Pfannex/ADE7953_Breakoutboard/Pics/AP_config.PNG

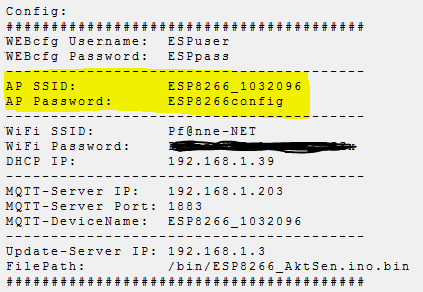
Pics/AP_config.PNG
