Pfannex/ADE7953_Breakoutboard/Pics/Cal_Energy_Graph.jpeg

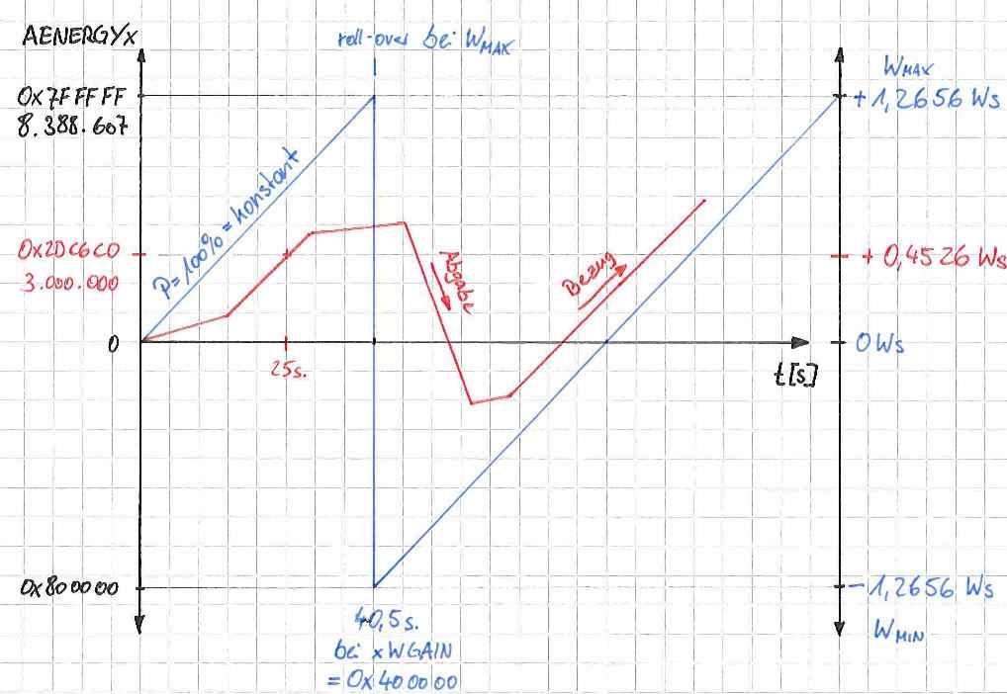
Pics/Cal_Energy_Graph.jpeg
