Pfannex/ADE7953_Breakoutboard/Pics/PGA.PNG

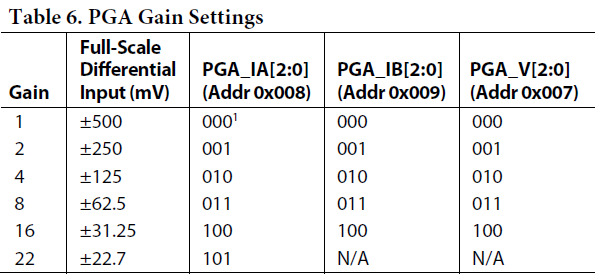
Pics/PGA.PNG
