Pfannex/ADE7953_Breakoutboard/Pics/read_return.PNG

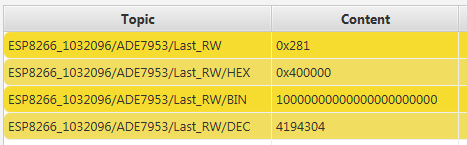
Pics/read_return.PNG
