Pfannex/ADE7953_Breakoutboard/Pics/WebIF_all.PNG

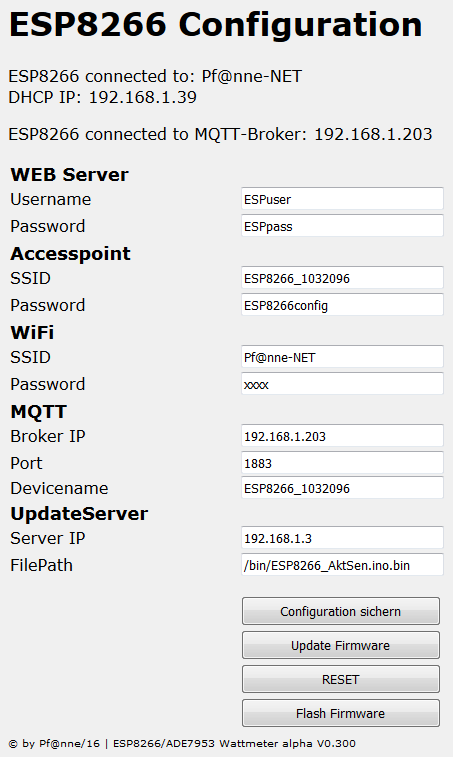
Pics/WebIF_all.PNG
