Pfannex/ADE7953_Breakoutboard/Pics/writeBit_return.PNG

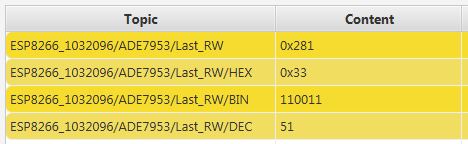
Pics/writeBit_return.PNG
