Pfannex/ADE7953_Breakoutboard/ESP8266_Basic_webServer.cpp

/******************************************************************************

  ProjectName: ESP8266 Basic template             ***** *****
  SubTitle   : WebServer routines                *     *     ************
                                                *   **   **   *           *
  Copyright by Pf@nne                          *   *   *   *   *   ****    *
                                               *   *       *   *   *   *   *
  Last modification by:                        *   *       *   *   ****    *
  - Pf@nne (pf@nne-mail.de)                     *   *     *****           *
                                                 *   *        *   *******
  Date    : 03.12.2016                            *****      *   *
  Version : alpha 0.200                                     *   *
  Revison :                                                *****

********************************************************************************/
#include "ESP8266_Basic_webServer.h"

ESP8266_Basic_webServer::ESP8266_Basic_webServer() : webServer(80){ 

  httpUpdater.setup(&webServer); 
 
  webServer.on("/", std::bind(&ESP8266_Basic_webServer::rootPageHandler, this));
  webServer.on("/ADE7953", std::bind(&ESP8266_Basic_webServer::ADE7953PageHandler, this));
  
  webServer.on("/wlan_config", std::bind(&ESP8266_Basic_webServer::wlanPageHandler, this));
  webServer.on("/gpio", std::bind(&ESP8266_Basic_webServer::gpioPageHandler, this));
  //webServer.on("/cfg", std::bind(&ESP8266_Basic_webServer::cfgPageHandler, this));
  webServer.onNotFound(std::bind(&ESP8266_Basic_webServer::handleNotFound, this));
}

//===============================================================================
//  WEB-Server control
//===============================================================================
void ESP8266_Basic_webServer::start(){
  Serial.println("Start WEB-Server");
  
  pinMode(GPIO2, OUTPUT);
  webServer.begin(); 
  Serial.println("HTTP server started");

}
//===> handle WEB-Server <-----------------------------------------------------
void ESP8266_Basic_webServer::handleClient(){
   webServer.handleClient();
}
//===> CFGstruct pointer <-----------------------------------------------------
void ESP8266_Basic_webServer::set_cfgPointer(CFG *p){
  cfg = p;
}
//===> Sesorstruct pointer <---------------------------------------------------
/*void ESP8266_Basic_webServer::set_sensorPointer(TDS18B20_Sensors *p, THTU21_Sensors *q, TBMP180_Sensors *r){
  DS18B20_Sensors = p;
  HTU21_Sensors = q;
  BMP180_Sensors = r;
}*/
//===> Callback for CFGchange <------------------------------------------------
void ESP8266_Basic_webServer::set_saveConfig_Callback(CallbackFunction c){
  saveConfig_Callback = c;
}
//===> Update Firmware <-------------------------------------------------------
void ESP8266_Basic_webServer::updateFirmware(){
  Serial.println("Updating Firmware.......");
  t_httpUpdate_return ret = ESPhttpUpdate.update(cfg->updateServer, 80, cfg->filePath);
  switch(ret) {
    case HTTP_UPDATE_FAILED:
        Serial.println("[update] Update failed.");
        break;
    case HTTP_UPDATE_NO_UPDATES:
        Serial.println("[update] Update no Update.");
        break;
    case HTTP_UPDATE_OK:
        Serial.println("[update] Update ok."); // may not called we reboot the ESP
        break;
  }
}

//===============================================================================
//  HTML handling
//===============================================================================

//===> Sensor Page <-------------------------------------------------------
void ESP8266_Basic_webServer::ADE7953PageHandler(){
 String rm = ""
  
  "<!doctype html> <html>"
  "<head> <meta charset='utf-8'>"
  "<meta http-equiv='refresh' content='5; URL=http://" + String(IPtoString(WiFi.localIP()))  + "/ADE7953'>"
  "<title>ESP8266 Sensoren</title>"
  "</head>"

  "<body><body bgcolor='#F0F0F0'><font face='VERDANA,ARIAL,HELVETICA'> <form> <font face='VERDANA,ARIAL,HELVETICA'>"
  "<b><h1>ADE7953 measurement</h1></b>"
  
  "<b><h3>Voltage / Current</h3></b>";
  
	  rm += "<font face='Courier New'>";
	
	  //rm += "<tab indent=20>";
    rm += "Voltage : </b>";
    rm += "Current A : </b>";
    rm += "Current B : </b>";
    //DS18B20_Sensors->item[i].serial

  rm += "</font></p>"
  "<font face='VERDANA,ARIAL,HELVETICA'> <b><h3>Power</h3></b> </font>";
  
    rm += "Power : </b>";
    rm += "Q : </b>";
    rm += "S : </b>";


  rm += "</font></p>"
  "<font face='VERDANA,ARIAL,HELVETICA'><font size='-2'>&copy; by Pf@nne/16   |   " + String(cfg->version) + "</font>"
  "</body bgcolor> </body></font>"
  "</html>"  
  ;

  webServer.send(200, "text/html", rm);

}

//#############################################################################
void ESP8266_Basic_webServer::rootPageHandler()
{
  // Check if there are any GET parameters
  if (webServer.hasArg("webUser")) strcpy(cfg->webUser, webServer.arg("webUser").c_str());
  if (webServer.hasArg("webPassword")) strcpy(cfg->webPassword, webServer.arg("webPassword").c_str());
  if (webServer.hasArg("apName")) strcpy(cfg->apName, webServer.arg("apName").c_str());
  if (webServer.hasArg("apPassword")) strcpy(cfg->apPassword, webServer.arg("apPassword").c_str());
  if (webServer.hasArg("wifiSSID")) strcpy(cfg->wifiSSID, webServer.arg("wifiSSID").c_str());
  if (webServer.hasArg("wifiPSK")) strcpy(cfg->wifiPSK, webServer.arg("wifiPSK").c_str());
  if (webServer.hasArg("wifiIP")) strcpy(cfg->wifiIP, webServer.arg("wifiIP").c_str());
  if (webServer.hasArg("mqttServer")) strcpy(cfg->mqttServer, webServer.arg("mqttServer").c_str());
  if (webServer.hasArg("mqttPort")) strcpy(cfg->mqttPort, webServer.arg("mqttPort").c_str());
  if (webServer.hasArg("mqttDeviceName")) strcpy(cfg->mqttDeviceName, webServer.arg("mqttDeviceName").c_str());
  if (webServer.hasArg("updateServer")) strcpy(cfg->updateServer, webServer.arg("updateServer").c_str());
  if (webServer.hasArg("filePath")) strcpy(cfg->filePath, webServer.arg("filePath").c_str());
  

  String rm = ""
  
  "<!doctype html> <html>"
  "<head> <meta charset='utf-8'>"
  "<title>ESP8266 Configuration</title>"
  "</head>"

  "<body><body bgcolor='#F0F0F0'><font face='VERDANA,ARIAL,HELVETICA'> <form> <font face='VERDANA,ARIAL,HELVETICA'>"
  "<b><h1>ESP8266 Configuration</h1></b>";

  if (WiFi.status() == WL_CONNECTED){
    rm += "ESP8266 connected to: "; rm += WiFi.SSID(); rm += "<br>";
    rm += "DHCP IP: "; rm += String(IPtoString(WiFi.localIP())); rm += "<p></p>";
  }else{
    rm += "ESP8266 ist not connected!"; rm += "<p></p>";
  }	
  
  String str = String(cfg->mqttStatus);
  if (str == "connected"){
    rm += "ESP8266 connected to MQTT-Broker: "; rm += cfg->mqttServer; rm += "<p></p>";
  }

  rm += ""
  "<table width='30%' border='0' cellpadding='0' cellspacing='2'>"
  " <tr>"
  "  <td><b><font size='+1'>WEB Server</font></b></td>"
  "  <td></td>"
  " </tr>"
  " <tr>"
  "  <td>Username</td>"
  "  <td><input type='text' id='webUser' name='webUser' value='" + String(cfg->webUser) + "' size='30' maxlength='40' placeholder='Username'></td>"
  " </tr>"
  " <tr>"
  " <tr>"
  "  <td>Password</td>"
  "  <td><input type='text' id='webPassword' name='webPassword' value='" + String(cfg->webPassword) + "' size='30' maxlength='40' placeholder='Password'></td>"
  " </tr>"
  " <tr>"

  " <tr>"
  "  <td><b><font size='+1'>Accesspoint</font></b></td>"
  "  <td></td>"
  " </tr>"
  " <tr>"
  "  <td>SSID</td>"
  "  <td><input type='text' id='apName' name='apName' value='" + String(cfg->apName) + "' size='30' maxlength='40' placeholder='SSID'></td>"
  " </tr>"
  " <tr>"
  " <tr>"
  "  <td>Password</td>"
  "  <td><input type='text' id='apPassword' name='apPassword' value='" + String(cfg->apPassword) + "' size='30' maxlength='40' placeholder='Password'></td>"
  " </tr>"
  " <tr>"

  " <tr>"
  "  <td><b><font size='+1'>WiFi</font></b></td>"
  "  <td></td>"
  " </tr>"
  "  <td>SSID</td>"
  "  <td><input type='text' id='wifiSSID' name='wifiSSID' value='" + String(cfg->wifiSSID) + "' size='30' maxlength='40' placeholder='SSID'></td>"
  " </tr>"
  " <tr>"
  " <tr>"
  "  <td>Password</td>"
  "  <td><input type='text' id='wifiPSK' name='wifiPSK' value='" + String(cfg->wifiPSK) + "' size='30' maxlength='40' placeholder='Password'></td>"
  " </tr>"
  " <tr>"

  " <tr>"
  "  <td><b><font size='+1'>MQTT</font></b></td>"
  "  <td></td>"
  " </tr>"
  " <tr>"
  "  <td>Broker IP</td>"
  "  <td><input type='text' id='mqttServer' name='mqttServer' value='" + String(cfg->mqttServer) + "' size='30' maxlength='40' placeholder='IP Address'></td>"
  " </tr>"
  " <tr>"
  " <tr>"
  "  <td>Port</td>"
  "  <td><input type='text' id='mqttPort' name='mqttPort' value='" + String(cfg->mqttPort) + "' size='30' maxlength='40' placeholder='Port'></td>"
  " </tr>"
  " <tr>"
  "  <td>Devicename</td>"
  "  <td><input type='text' id='mqttDeviceName' name='mqttDeviceName' value='" + String(cfg->mqttDeviceName) + "' size='30' maxlength='40' placeholder='Devicename'></td>"
  " </tr>"

  " <tr>"
  "  <td><b><font size='+1'>UpdateServer</font></b></td>"
  "  <td></td>"
  " </tr>"
  " <tr>"
  "  <td>Server IP</td>"
  "  <td><input type='text' id='updateServer' name='updateServer' value='" + String(cfg->updateServer) + "' size='30' maxlength='40' placeholder='IP Address'></td>"
  " </tr>"
  " <tr>"
  " <tr>"
  "  <td>FilePath</td>"
  "  <td><input type='text' id='filePath' name='filePath' value='" + String(cfg->filePath) + "' size='30' maxlength='40' placeholder='Path'></td>"
  " </tr>"

  " <tr>"
  "  <td><p></p> </td>"
  "  <td>  </td>"
  " </tr>"
  " <tr>"
  "  <td></td>"
  "  <td><input type='submit' value='Configuration sichern' style='height:30px; width:200px' > </font></form> </td>"
  " </tr>"

 " <tr>"
 "  <td></td>"
 "  <td>  </td>"
 " </tr>"
 " <tr>"
 "  <td></td>"
 "  <td><input type='submit' value='Update Firmware' id='update' name='update' value='' style='height:30px; width:200px' ></td>"
 " </tr>"

  " <tr>"
  "  <td></td>"
  "  <td>  </td>"
  " </tr>"
  " <tr>"
  "  <td></td>"
  "  <td><input type='submit' value='RESET' id='reset' name='reset' value='' style='height:30px; width:200px' >  </font></form> </td>"
  " </tr>"

  " <tr>"
  "  <td></td>"
  "  <td>  </td>"
  " </tr>"
  " <tr>"
  "  <td></td>"
  "  <td><input type='button' onclick=\"location.href='./update'\"  value='Flash Firmware' style='height:30px; width:200px' >  </font></form> </td>"
  " </tr>"

  "</table>"

  "<font size='-2'>&copy; by Pf@nne/16   |   " + String(cfg->version) + "</font>"
  "</body bgcolor> </body></font>"
  "</html>"  
  ;

  webServer.send(200, "text/html", rm);
 
  if (saveConfig_Callback != nullptr)
    saveConfig_Callback();
  else
     Serial.println("null");
	 
  if (webServer.hasArg("reset")) ESP.restart();
  if (webServer.hasArg("update")) updateFirmware();
}

//#############################################################################

void ESP8266_Basic_webServer::wlanPageHandler()
{
  // Check if there are any GET parameters
  if (webServer.hasArg("ssid"))
  {    
    if (webServer.hasArg("password"))
    {
      WiFi.begin(webServer.arg("ssid").c_str(), webServer.arg("password").c_str());
    }
    else
    {
      WiFi.begin(webServer.arg("ssid").c_str());
    }
    
    while (WiFi.status() != WL_CONNECTED)
    {
      delay(500);
      Serial.print(".");
    }
      
    Serial.println("");
    Serial.println("WiFi connected");  
    Serial.println("IP address: ");
    Serial.println(WiFi.localIP());

    delay(1000);
  }
  
  String response_message = "";
  response_message += "<html>";
  response_message += "<head><title>ESP8266 Webserver</title></head>";
  response_message += "<body style=\"background-color:PaleGoldenRod\"><h1><center>WLAN Settings</center></h1>";
  
  if (WiFi.status() == WL_CONNECTED)
  {
    response_message += "Status: Connected<br>";
  }
  else
  {
    response_message += "Status: Disconnected<br>";
  }
  
  response_message += "<p>To connect to a WiFi network, please select a network...</p>";

  // Get number of visible access points
  int ap_count = WiFi.scanNetworks();
  
  if (ap_count == 0)
  {
    response_message += "No access points found.<br>";
  }
  else
  {
    response_message += "<form method=\"get\">";

    // Show access points
    for (uint8_t ap_idx = 0; ap_idx < ap_count; ap_idx++)
    {
      response_message += "<input type=\"radio\" name=\"ssid\" value=\"" + String(WiFi.SSID(ap_idx)) + "\">";
      response_message += String(WiFi.SSID(ap_idx)) + " (RSSI: " + WiFi.RSSI(ap_idx) +")";
      (WiFi.encryptionType(ap_idx) == ENC_TYPE_NONE) ? response_message += " " : response_message += "*";
      response_message += "<br><br>";
    }
    
    response_message += "WiFi password (if required):<br>";
    response_message += "<input type=\"text\" name=\"password\"><br>";
    response_message += "<input type=\"submit\" value=\"Connect\">";
    response_message += "</form>";
  }

  response_message += "</body></html>";
  
  webServer.send(200, "text/html", response_message);
}


void ESP8266_Basic_webServer::gpioPageHandler()
{
  // Check if there are any GET parameters
  if (webServer.hasArg("gpio2"))
  { 
    if (webServer.arg("gpio2") == "1")
    {
      digitalWrite(GPIO2, HIGH);
    }
    else
    {
      digitalWrite(GPIO2, LOW);
    }
  }

  String response_message = "<html><head><title>ESP8266 Webserver</title></head>";
  response_message += "<body style=\"background-color:PaleGoldenRod\"><h1><center>Control GPIO pins</center></h1>";
  response_message += "<form method=\"get\">";

  response_message += "GPIO2:<br>";

  if (digitalRead(GPIO2) == LOW)
  {
    response_message += "<input type=\"radio\" name=\"gpio2\" value=\"1\" onclick=\"submit();\">On<br>";
    response_message += "<input type=\"radio\" name=\"gpio2\" value=\"0\" onclick=\"submit();\" checked>Off<br>";
  }
  else
  {
    response_message += "<input type=\"radio\" name=\"gpio2\" value=\"1\" onclick=\"submit();\" checked>On<br>";
    response_message += "<input type=\"radio\" name=\"gpio2\" value=\"0\" onclick=\"submit();\">Off<br>";
  }

  response_message += "</form></body></html>";

  
  webServer.send(200, "text/html", response_message);
}


void ESP8266_Basic_webServer::handleNotFound()
{
  String message = "File Not Found\n\n";
  message += "URI: ";
  message += webServer.uri();
  message += "\nMethod: ";
  message += (webServer.method() == HTTP_GET)?"GET":"POST";
  message += "\nArguments: ";
  message += webServer.args();
  message += "\n";
  
  for (uint8_t i = 0; i < webServer.args(); i++)
  {
    message += " " + webServer.argName(i) + ": " + webServer.arg(i) + "\n";
  }
  
  webServer.send(404, "text/plain", message);
}

//===============================================================================
//  helpers
//===============================================================================

//===> IPToString  <-----------------------------------------------------------
String ESP8266_Basic_webServer::IPtoString(IPAddress ip) {
  String res = "";
  for (int i = 0; i < 3; i++) {
    res += String((ip >> (8 * i)) & 0xFF) + ".";
  }
  res += String(((ip >> 8 * 3)) & 0xFF);
  return res;
}
