Pfannex/ADE7953_Breakoutboard/ESP8266_Basic_data.cpp

/******************************************************************************

  ProjectName: ESP8266 Basic template             ***** *****
  SubTitle   : Data definitions                  *     *     ************
                                                *   **   **   *           *
  Copyright by Pf@nne                          *   *   *   *   *   ****    *
                                               *   *       *   *   *   *   *
  Last modification by:                        *   *       *   *   ****    *
  - Pf@nne (pf@nne-mail.de)                     *   *     *****           *
                                                 *   *        *   *******
  Date    : 03.12.2016                            *****      *   *
  Version : alpha 0.200                                     *   *
  Revison :                                                *****

********************************************************************************/
#include <Arduino.h>
#include "ESP8266_Basic_data.h"

Topics::Topics(){ 

//suscibe
  sub.E1.count = sub_e1;
  sub.E2.count = sub_e2;
  sub.E3.count = sub_e3;
  
  sub.E1.item[0] = "WiFiConfig";
  sub.E2.item[0][0] = "WEBserver";
  sub.E3.item[0][0][0] = "Username";
  sub.E3.item[0][0][1] = "Password";
  sub.E2.item[0][1] = "Accesspoint";
  sub.E3.item[0][1][0] = "SSID";
  sub.E3.item[0][1][1] = "Password";
  sub.E2.item[0][2] = "WiFi";
  sub.E3.item[0][2][0] = "SSID";
  sub.E3.item[0][2][1] = "Password";
  sub.E3.item[0][2][2] = "IP";
  sub.E2.item[0][3] = "MQTT";
  sub.E3.item[0][3][0] = "Server";
  sub.E3.item[0][3][1] = "Port";
  sub.E3.item[0][3][2] = "Status";
  sub.E2.item[0][4] = "UpdateServer";
  sub.E3.item[0][4][0] = "Server";
  sub.E3.item[0][4][1] = "FilePath";
    
  sub.E1.item[1] = "ESP8266";
  sub.E2.item[1][0] = "Control";
  sub.E3.item[1][0][0] = "Reboot";

  sub.E1.item[2] = "ADE7953";
  sub.E2.item[2][0] = "Control";
  sub.E3.item[2][0][1] = "read";
  sub.E3.item[2][0][2] = "write";
  sub.E3.item[2][0][3] = "readBit";
  sub.E3.item[2][0][4] = "writeBit";
  sub.E3.item[2][0][5] = "init";
  sub.E3.item[2][0][6] = "updateTime";
  sub.E3.item[2][0][7] = "saveConfig";
  sub.E3.item[2][0][8] = "setDefault";
  sub.E3.item[2][0][9] = "resetEnergy";
  sub.E2.item[2][1] = "getValues";
  sub.E3.item[2][1][0] = "V_INST";
  sub.E3.item[2][1][1] = "IA_INST";
  sub.E3.item[2][1][2] = "IB_INST";
  sub.E3.item[2][1][3] = "getWaves";
  sub.E3.item[2][1][4] = "SampleRate";
  sub.E3.item[2][1][5] = "Periods";

  sub.E1.item[3] = "File";
  sub.E2.item[3][0] = "Read";
  sub.E3.item[3][0][0] = "Field_01";
  sub.E3.item[3][0][1] = "Field_02";
  sub.E2.item[3][1] = "Write";
  sub.E3.item[3][1][0] = "Field_01";
  sub.E3.item[3][1][1] = "Field_02";

  sub.E1.item[4] = "Relay";
  sub.E2.item[4][0] = "set";
  sub.E2.item[4][1] = "getStatus";

//publish
  pub.E1.count = pub_e1;
  pub.E2.count = pub_e2;
  pub.E3.count = pub_e3;
  
  pub.E1.item[0] = "WiFiConfig";
  pub.E2.item[0][0] = "WEBserver";
  pub.E3.item[0][0][0] = "Username";
  pub.E3.item[0][0][1] = "Password";
  pub.E2.item[0][1] = "Accesspoint";
  pub.E3.item[0][1][0] = "SSID";
  pub.E3.item[0][1][1] = "Password";
  pub.E2.item[0][2] = "WiFi";
  pub.E3.item[0][2][0] = "SSID";
  pub.E3.item[0][2][1] = "Password";
  pub.E3.item[0][2][2] = "IP";
  pub.E2.item[0][3] = "MQTT";
  pub.E3.item[0][3][0] = "Server";
  pub.E3.item[0][3][1] = "Port";
  pub.E3.item[0][3][2] = "Status";
  pub.E2.item[0][4] = "UpdateServer";
  pub.E3.item[0][4][0] = "Server";
  pub.E3.item[0][4][1] = "FilePath";
  
  pub.E1.item[1] = "Control";
  pub.E2.item[1][0] = "Status";
  pub.E3.item[1][0][0] = "WiFi";
  pub.E3.item[1][0][1] = "MQTT";
  pub.E3.item[1][0][2] = "updateFirmware";

  pub.E1.item[2] = "ADE7953";
  pub.E2.item[2][0] = "Last_RW";
  pub.E3.item[2][0][0] = "HEX";
  pub.E3.item[2][0][1] = "BIN";
  pub.E3.item[2][0][2] = "DEC";
  pub.E3.item[2][0][3] = "Bit";
  pub.E3.item[2][0][4] = "value";
  pub.E3.item[2][0][5] = "RegName";
  pub.E2.item[2][1] = "values";
  pub.E3.item[2][1][0] = "V_RMS";
  pub.E3.item[2][1][1] = "IA_RMS";
  pub.E3.item[2][1][2] = "IB_RMS";
  pub.E3.item[2][1][3] = "PFA";
  pub.E3.item[2][1][4] = "PFB";
  pub.E3.item[2][1][5] = "ANGLE_A";
  pub.E3.item[2][1][6] = "ANGLE_B";
  pub.E3.item[2][1][7] = "PERIOD";
  pub.E3.item[2][1][8] = "FREQUENZ";
  pub.E3.item[2][1][9] = "P_A";
  pub.E3.item[2][1][10] = "Q_A";
  pub.E3.item[2][1][11] = "S_A";
  pub.E3.item[2][1][12] = "P_B";
  pub.E3.item[2][1][13] = "Q_B";
  pub.E3.item[2][1][14] = "S_B";
  pub.E3.item[2][1][15] = "IA_INST";
  pub.E3.item[2][1][16] = "IB_INST";
  pub.E3.item[2][1][17] = "V_INST";
  pub.E3.item[2][1][18] = "V_RMSrel";
  pub.E3.item[2][1][19] = "IA_RMSrel";
  pub.E3.item[2][1][20] = "IB_RMSrel";
  pub.E3.item[2][1][21] = "P_Arel";
  pub.E3.item[2][1][22] = "Q_Arel";
  pub.E3.item[2][1][23] = "S_Arel";
  pub.E3.item[2][1][24] = "P_Brel";
  pub.E3.item[2][1][25] = "Q_Brel";
  pub.E3.item[2][1][26] = "S_Brel";
  pub.E3.item[2][1][27] = "W_A";
  pub.E3.item[2][1][28] = "Wb_A";
  pub.E3.item[2][1][29] = "Ws_A";
  pub.E3.item[2][1][30] = "W_B";
  pub.E3.item[2][1][31] = "Wb_B";
  pub.E3.item[2][1][32] = "Ws_B";
  pub.E3.item[2][1][33] = "Time";
  pub.E3.item[2][1][34] = "INSTready";
  pub.E3.item[2][1][35] = "temperature";
  pub.E3.item[2][1][36] = "pressure";

  pub.E1.item[3] = "Relay";
  pub.E2.item[3][0] = "state";



}
