Pfannex/ADE7953_Breakoutboard/ESP8266_Basic_data.h

/******************************************************************************

  ProjectName: ESP8266 Basic template             ***** *****
  SubTitle   : Data Header                       *     *     ************
                                                *   **   **   *           *
  Copyright by Pf@nne                          *   *   *   *   *   ****    *
                                               *   *       *   *   *   *   *
  Last modification by:                        *   *       *   *   ****    *
  - Pf@nne (pf@nne-mail.de)                     *   *     *****           *
                                                 *   *        *   *******
  Date    : 03.12.2016                            *****      *   *
  Version : alpha 0.200                                     *   *
  Revison :                                                *****

********************************************************************************/
#pragma once
#define Version "ESP8266/ADE7953 Wattmeter alpha V0.300"
 
  typedef char* topicField; 

//publish struct
  const int pub_e1 = 5;			//define TreeDepht here!!!
  const int pub_e2 = 6;
  const int pub_e3 = 50;
  const int pub_e4 = 0;
  
  typedef struct Tpub_topicE1{
    topicField item[pub_e1];
	int count;
  };
  typedef struct Tpub_topicE2{
    topicField item[pub_e1][pub_e2];
	int count;
  };
  typedef struct Tpub_topicE3{
    topicField item[pub_e1][pub_e2][pub_e3];
	int count;
  };
 
  typedef struct Tpub_Topic{
    Tpub_topicE1 E1;
    Tpub_topicE2 E2;
    Tpub_topicE3 E3;	
  };
  
//subscribe struct
  const int sub_e1 = 5;			//define TreeDepht here!!!
  const int sub_e2 = 6;
  const int sub_e3 = 10;
  const int sub_e4 = 0;
  
  typedef struct Tsub_topicE1{
    topicField item[sub_e1];
	int count;
  };
  typedef struct Tsub_topicE2{
    topicField item[sub_e1][sub_e2];
	int count;
  };
  typedef struct Tsub_topicE3{
    topicField item[sub_e1][sub_e2][sub_e3];
	int count;
  };
 
  typedef struct Tsub_Topic{
    Tsub_topicE1 E1;
    Tsub_topicE2 E2;
    Tsub_topicE3 E3;	
  };
  
 
class Topics{
public:
  Topics();
  Tpub_Topic pub; 
  Tsub_Topic sub; 
private:
}; 


// Config struct
  typedef struct CFG{
    char version[40] = Version;
    char webUser[40];
    char webPassword[40];
    char apName[40];
    char apPassword[40];
    char wifiSSID[40];
    char wifiPSK[40];
    char wifiIP[20];
    char mqttServer[20];
    char mqttPort[6];
    char mqttDeviceName[20];
	  char mqttStatus[20];
	  char updateServer[20];
	  char filePath[40];
  };
  
  typedef struct TdissectResult{
    bool found = false;
    String topic = "";
	  String value = "";
	  String itemPath = "";
	  int treeDepth = 0;
    int E1 = NULL;
    int E2 = NULL;
    int E3 = NULL;
    int E4 = NULL;   
  };
  
// MyFile struct
  typedef struct MyFile{
    char Field_01[15];
    char Field_02[15];
  };
 
// DS18B20 struct
  typedef struct TDS18B20_Sensor{
    char serial[30];
    char temperature[15];
  };
  
  typedef struct TDS18B20_Sensors{
    int count;
    TDS18B20_Sensor item[50]; 
  };

// HTU21 struct
  typedef struct THTU21_Sensor{
    int channel;
    char humidity[15];
    char temperature[15];
  };
  
  typedef struct THTU21_Sensors{
    int count;
    THTU21_Sensor item[10]; 
  };

// BMP180 struct
  typedef struct TBMP180_Sensor{
    int channel;
    char pressure[15];
    char temperature[15];
  };
  
  typedef struct TBMP180_Sensors{
    int count;
    TBMP180_Sensor item[10]; 
  };
  
